SedNavOrg/SedNav_Windsensor/software/src/tween_html.h

// JavaScript library tween-min.js.gz as HEX coded char array
// The char array is stored in the PROGRAM memory

constexpr char tween_min_js_gz[] PROGMEM = {
0x1F, 0x8B, 0x08, 0x00, 0x00, 0x00, 0x00, 0x00, 0x00, 0x03, 0xC5, 0x57, 0x4B, 0x73, 0xDB, 0x36, 
0x10, 0xBE, 0xE7, 0x57, 0xC8, 0x3E, 0x78, 0x00, 0x8A, 0xA4, 0x44, 0x26, 0x8A, 0x53, 0x49, 0xAC, 
0x0E, 0x4D, 0x32, 0xE3, 0x99, 0x64, 0xEA, 0x69, 0x7D, 0xF3, 0x78, 0x3C, 0xB4, 0x04, 0xC9, 0x68, 
0x15, 0x90, 0x03, 0x82, 0x76, 0x5C, 0x59, 0xFF, 0xBD, 0x8B, 0x17, 0x09, 0x3E, 0x64, 0x39, 0xE9, 
0xA1, 0x27, 0x02, 0xE0, 0xEE, 0xB7, 0xBB, 0x1F, 0x76, 0x17, 0xC0, 0x9B, 0x37, 0x23, 0xCF, 0xF3, 
0x06, 0x4B, 0xF6, 0xF0, 0xC4, 0xC3, 0x65, 0x51, 0x84, 0x9B, 0x7F, 0x06, 0xB0, 0x30, 0x7A, 0xB3, 
0x2E, 0xD9, 0x52, 0xD0, 0x8C, 0x0D, 0x3E, 0x92, 0x2D, 0xD9, 0xA4, 0x82, 0x20, 0xBC, 0xDB, 0xDB, 
0x71, 0xB8, 0xE4, 0x04, 0x3E, 0x89, 0x15, 0x42, 0xCC, 0x17, 0x78, 0xB7, 0xCE, 0x38, 0x7A, 0x48, 
0xF9, 0x80, 0x27, 0xD7, 0x37, 0x7E, 0x99, 0xA4, 0x7C, 0x53, 0x7E, 0x23, 0x4C, 0x14, 0xE1, 0x96, 
0xB0, 0x8D, 0xB8, 0xF7, 0x69, 0x12, 0xCF, 0xE8, 0xBC, 0x9C, 0xD1, 0xE1, 0x10, 0xF3, 0x6B, 0x1A, 
0xC4, 0x37, 0xB5, 0xCC, 0x35, 0xBD, 0x99, 0x71, 0x22, 0x4A, 0xCE, 0x06, 0x15, 0x28, 0xDE, 0x49, 
0x34, 0x0A, 0x68, 0xE1, 0x32, 0x63, 0xCB, 0x54, 0xA0, 0x4A, 0xDC, 0xE7, 0x78, 0x26, 0xC2, 0x34, 
0xCF, 0xB7, 0x4F, 0x60, 0x9B, 0xE2, 0xFD, 0xDE, 0xBF, 0x7A, 0x24, 0x84, 0x35, 0x3C, 0xF2, 0xA9, 
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
0xC8, 0xEA, 0xEC, 0x0C, 0x31, 0xA7, 0x1C, 0xCC, 0xD6, 0x4A, 0x2D, 0x64, 0x3D, 0x93, 0x95, 0xAF, 
0x87, 0xBA, 0xF4, 0xFD, 0x56, 0x05, 0x18, 0x2A, 0x75, 0xCE, 0x74, 0x89, 0x34, 0xFD, 0xC2, 0x14, 
0x8E, 0x42, 0x33, 0x4E, 0xB6, 0x35, 0x9A, 0x5B, 0xA5, 0x24, 0x87, 0x0E, 0x84, 0xD4, 0x92, 0xFD, 
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
};
